abdulwakeel12/DIY-FAB-Transistor-Tester/images/Electrical PCB.jpg

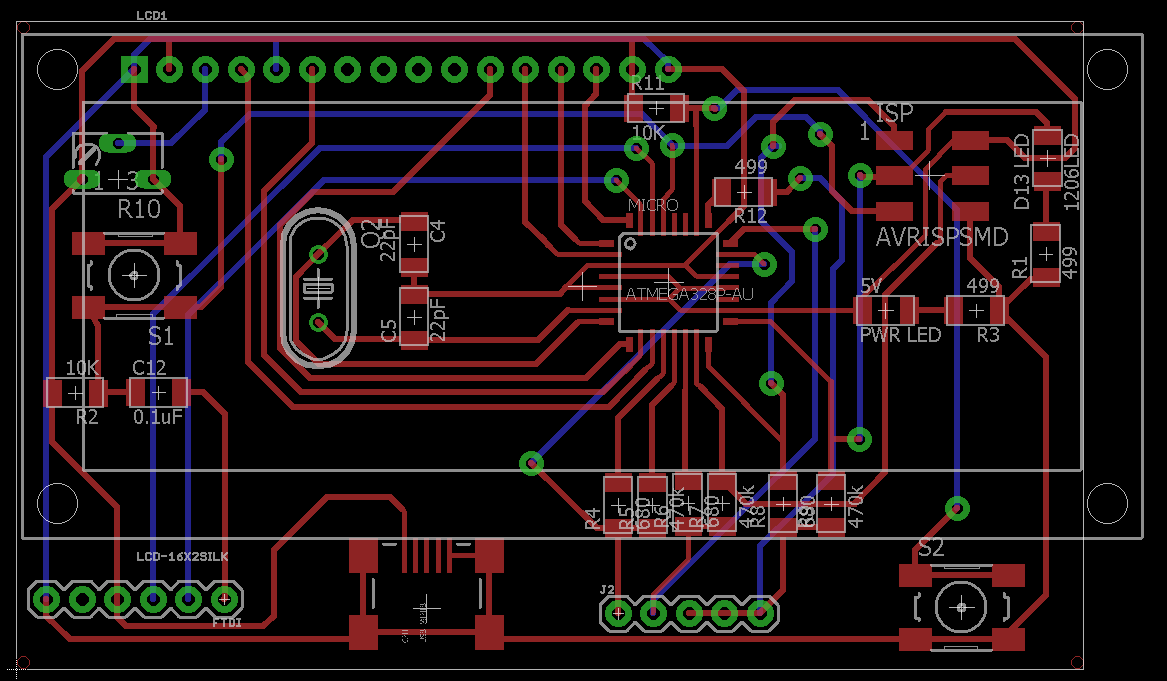
images/Electrical PCB.jpg
