abdulwakeel12/DIY-FAB-Transistor-Tester/images/Final Product 02.jpg

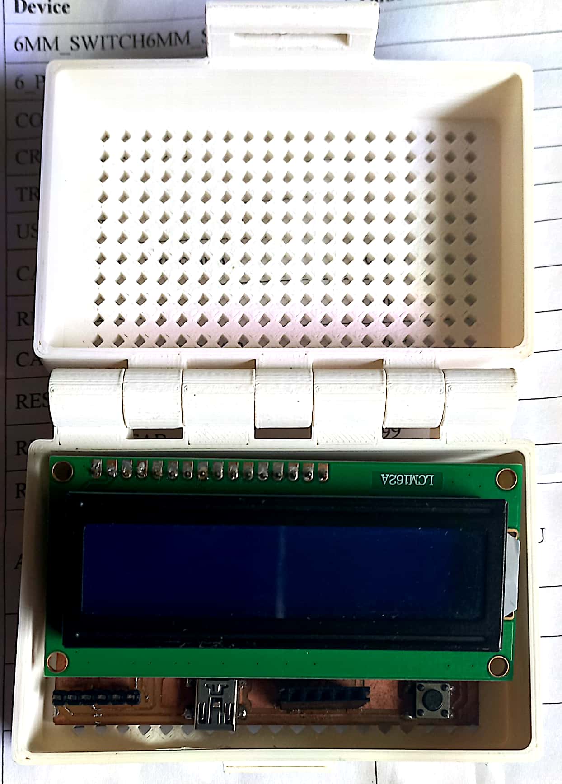
images/Final Product 02.jpg
