abdulwakeel12/DIY-FAB-Transistor-Tester/images/Final Product 03.jpg

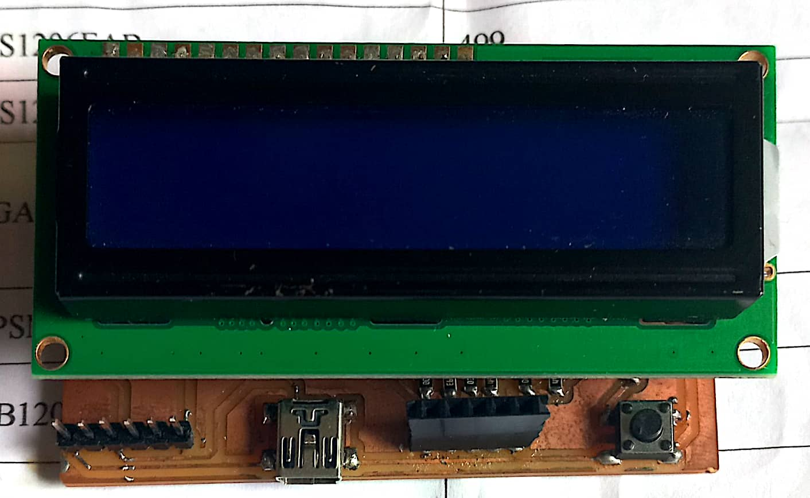
images/Final Product 03.jpg
