abdulwakeel12/DIY-FAB-Transistor-Tester/images/flow chart.jpg

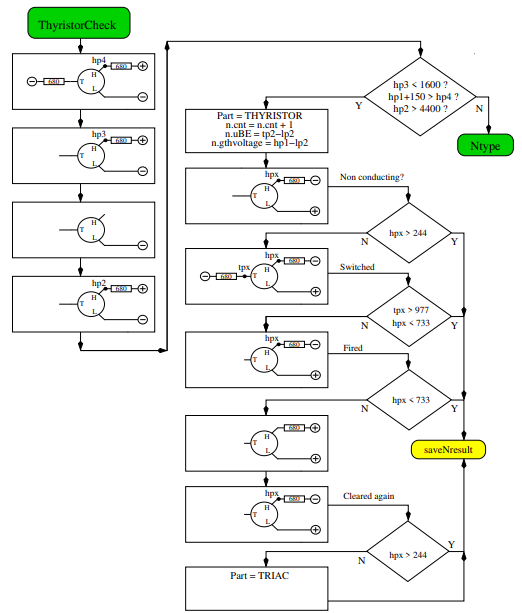
images/flow chart.jpg
