abdulwakeel12/DIY-FAB-Transistor-Tester/images/FTDI.jpg

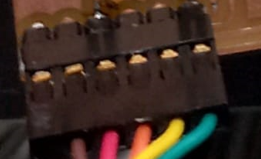
images/FTDI.jpg
