abdulwakeel12/DIY-FAB-Transistor-Tester/images/ICSP.jpg

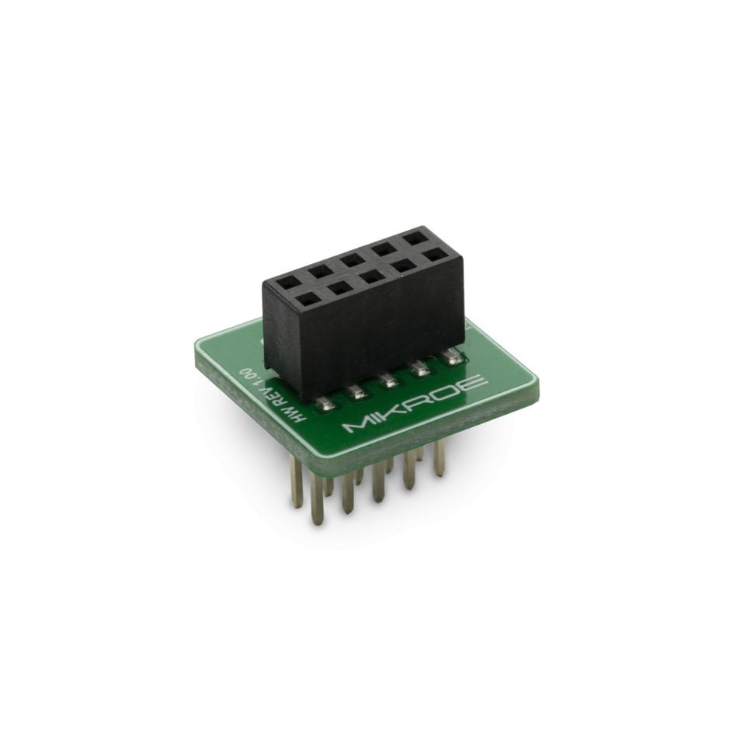
images/ICSP.jpg
