abdulwakeel12/DIY-FAB-Transistor-Tester/images/LCD.jpg

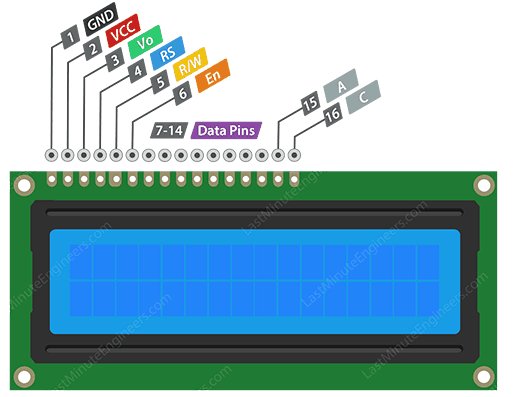
images/LCD.jpg
