abdulwakeel12/DIY-FAB-Transistor-Tester/images/Literature Review.jpg

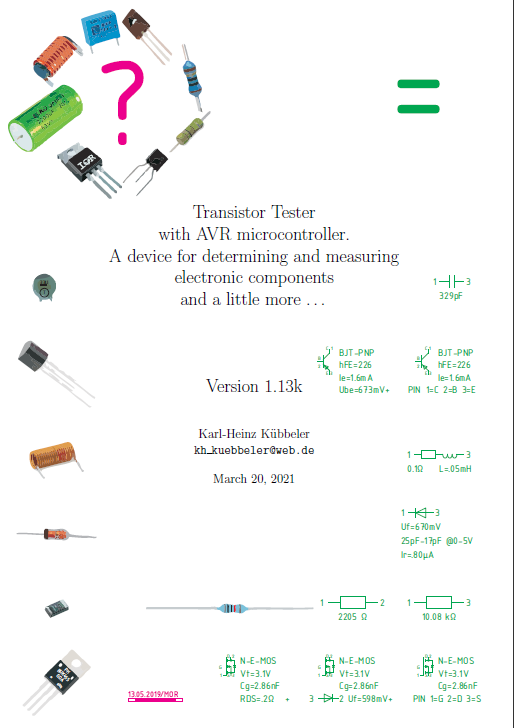
images/Literature Review.jpg
