abdulwakeel12/DIY-FAB-Transistor-Tester/images/Part 1.jpg

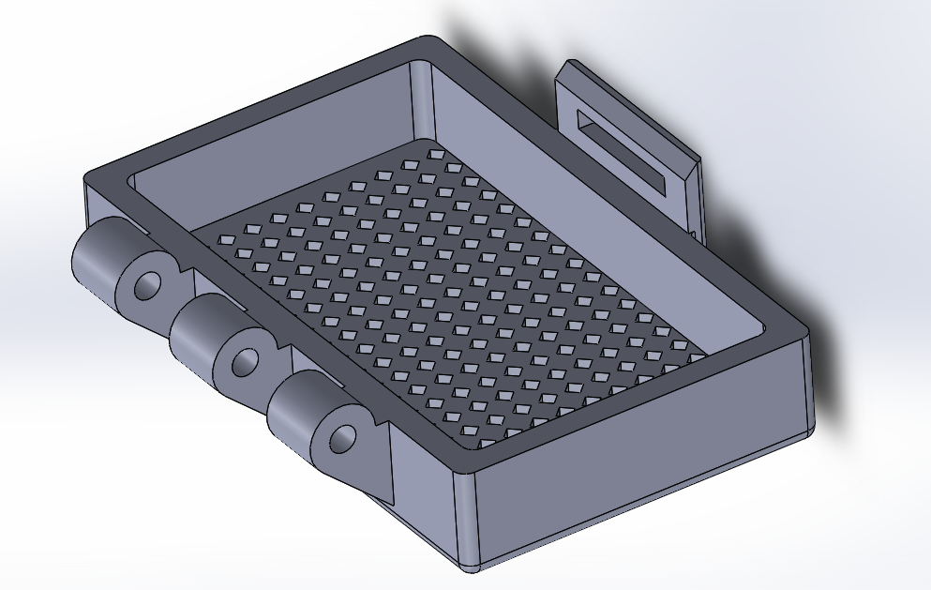
images/Part 1.jpg
