abdulwakeel12/DIY-FAB-Transistor-Tester/images/Part 2.jpg

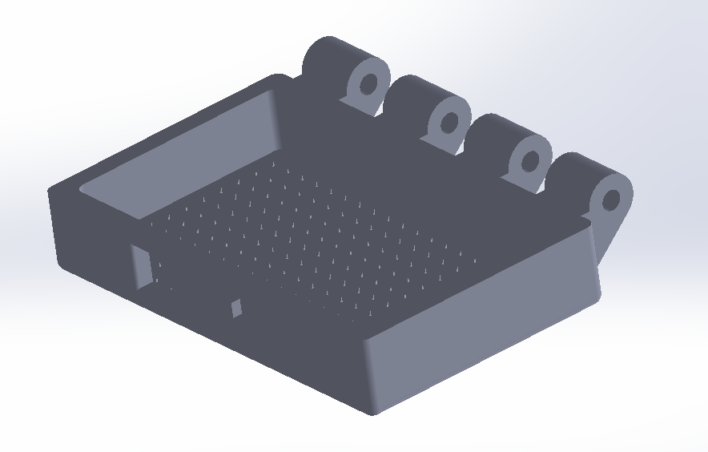
images/Part 2.jpg
