abdulwakeel12/DIY-FAB-Transistor-Tester/images/Part 3.jpg

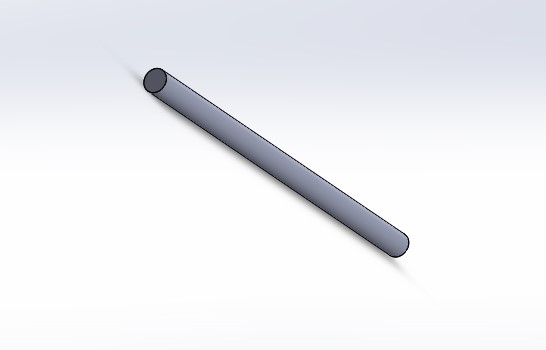
images/Part 3.jpg
