abdulwakeel12/DIY-FAB-Transistor-Tester/images/PCB Before Routing.jpg

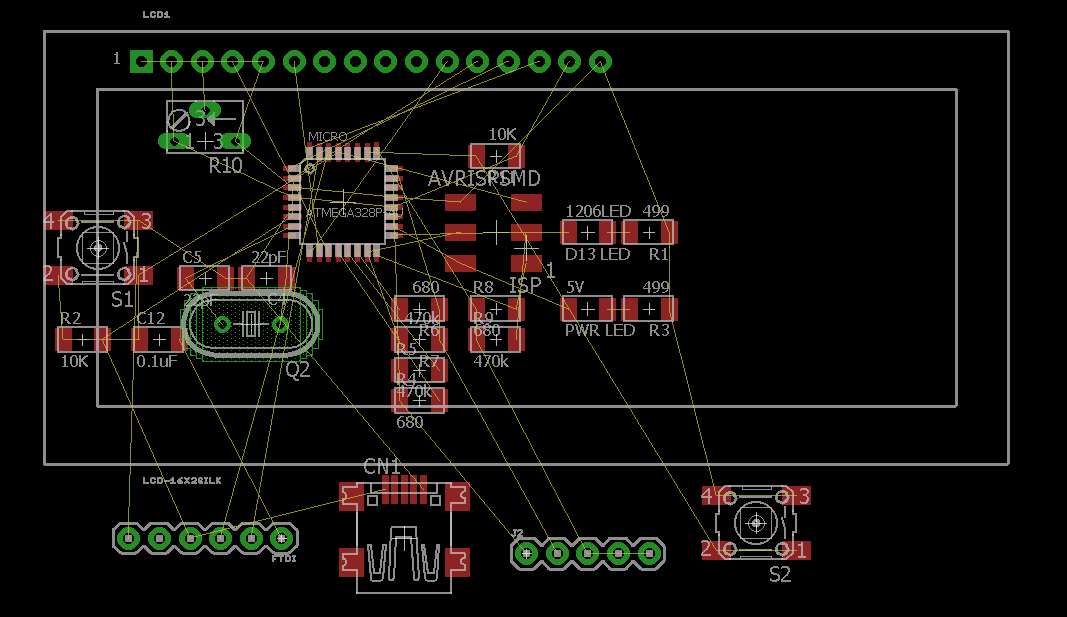
images/PCB Before Routing.jpg
