abdulwakeel12/DIY-FAB-Transistor-Tester/images/PCB BOTTOM.jpg

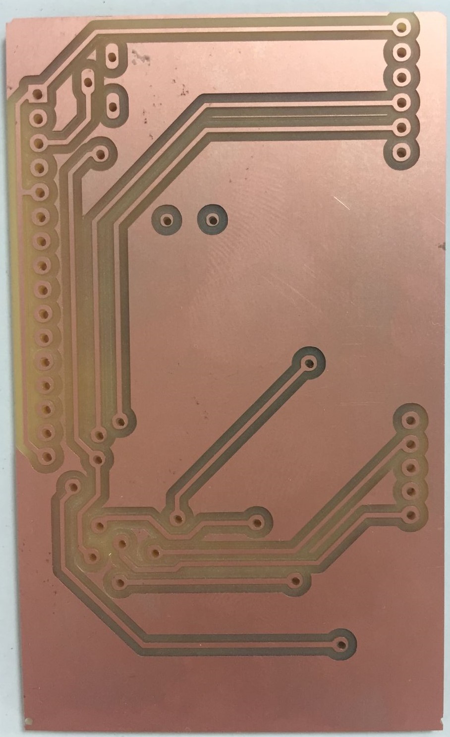
images/PCB BOTTOM.jpg
