abdulwakeel12/DIY-FAB-Transistor-Tester/images/PCB Top.jpg

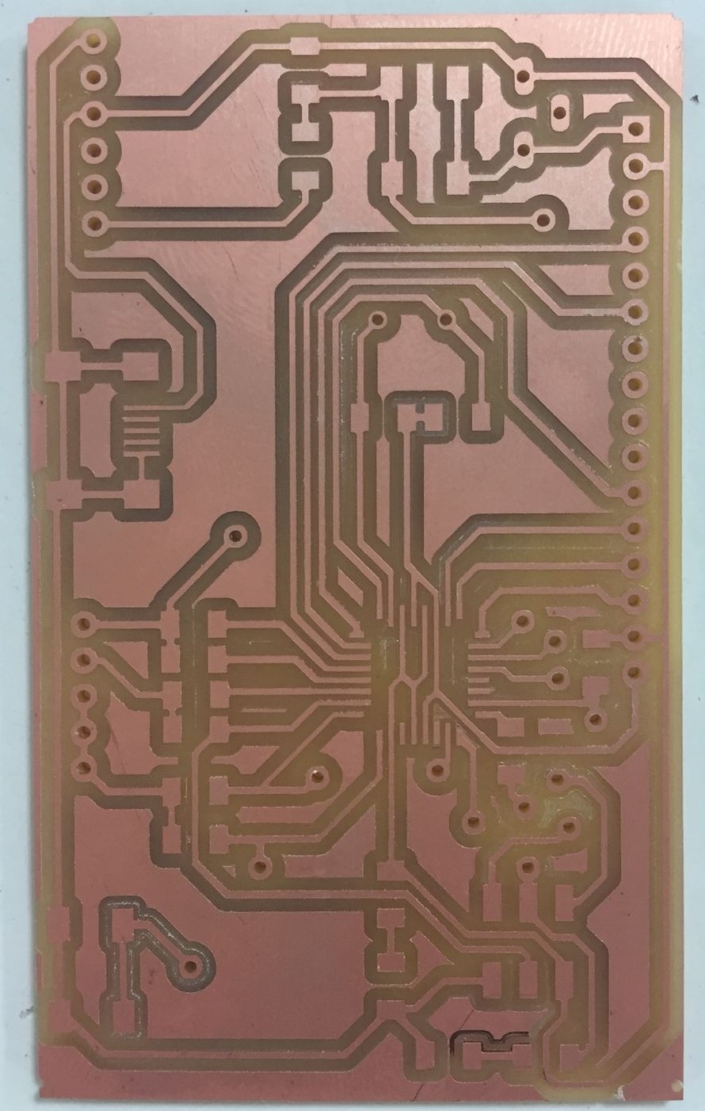
images/PCB Top.jpg
