abdulwakeel12/DIY-FAB-Transistor-Tester/images/Populated circuit.jpg

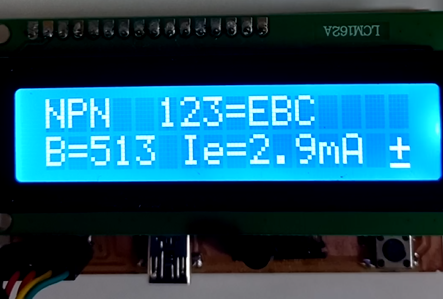
images/Populated circuit.jpg
