abdulwakeel12/DIY-FAB-Transistor-Tester/images/Populated pcb.jpg

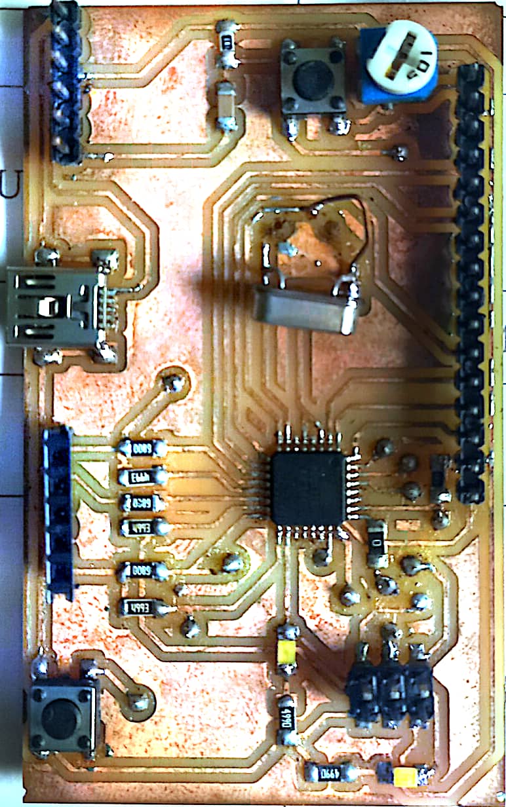
images/Populated pcb.jpg
