abdulwakeel12/DIY-FAB-Transistor-Tester/images/SRM Machine.jpg

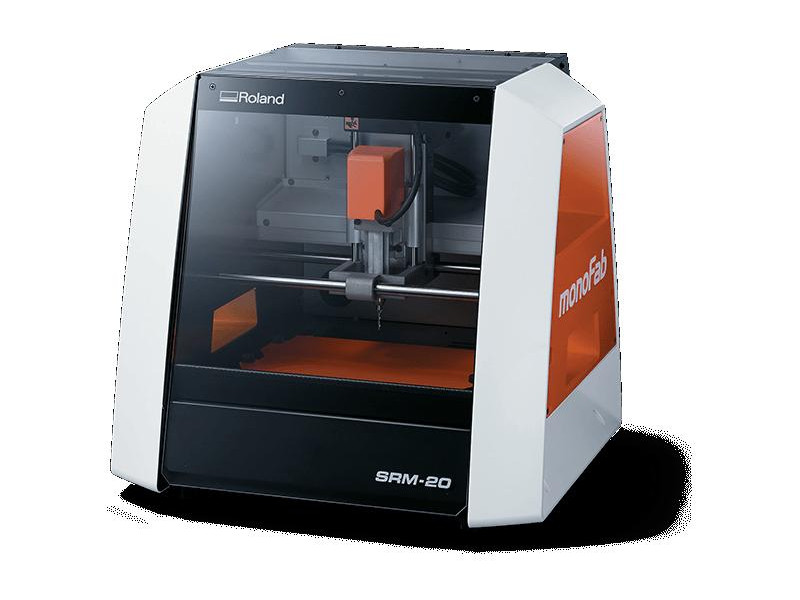
images/SRM Machine.jpg
