abdulwakeel12/DIY-FAB-Transistor-Tester/images/tactile.jpg

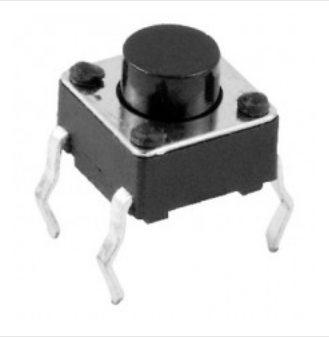
images/tactile.jpg
