abdulwakeel12/DIY-FAB-Transistor-Tester/images/Ultimaker in Lab.jpg

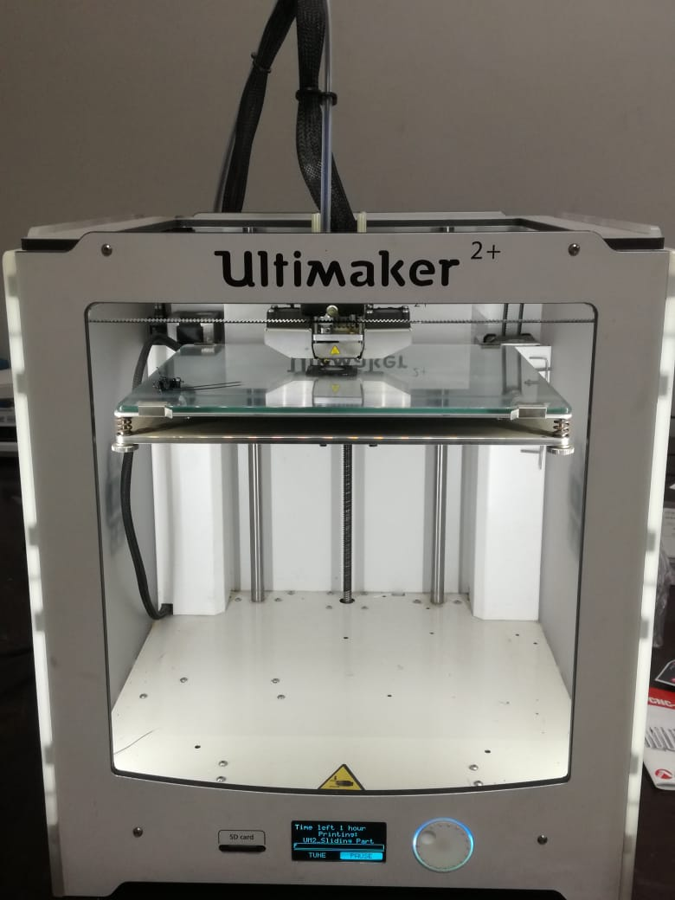
images/Ultimaker in Lab.jpg
