abdulwakeel12/DIY-FAB-Transistor-Tester/images/Ultimaker.jpg

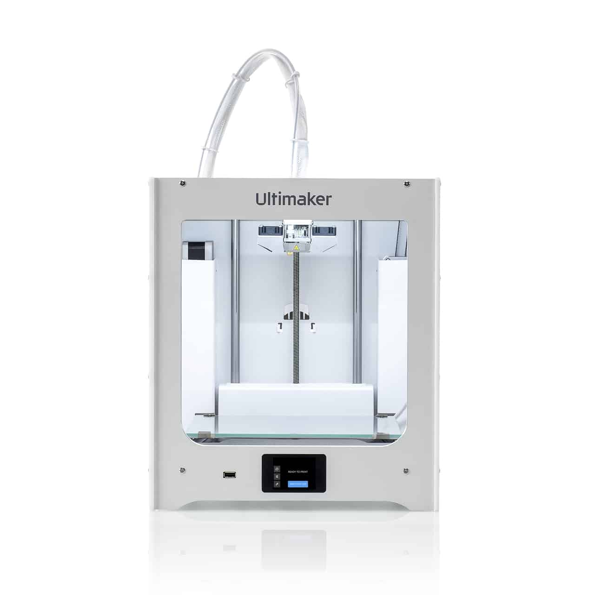
images/Ultimaker.jpg
