abdulwakeel12/DIY-FAB-Transistor-Tester/images/3D Printed Part 01.jpg

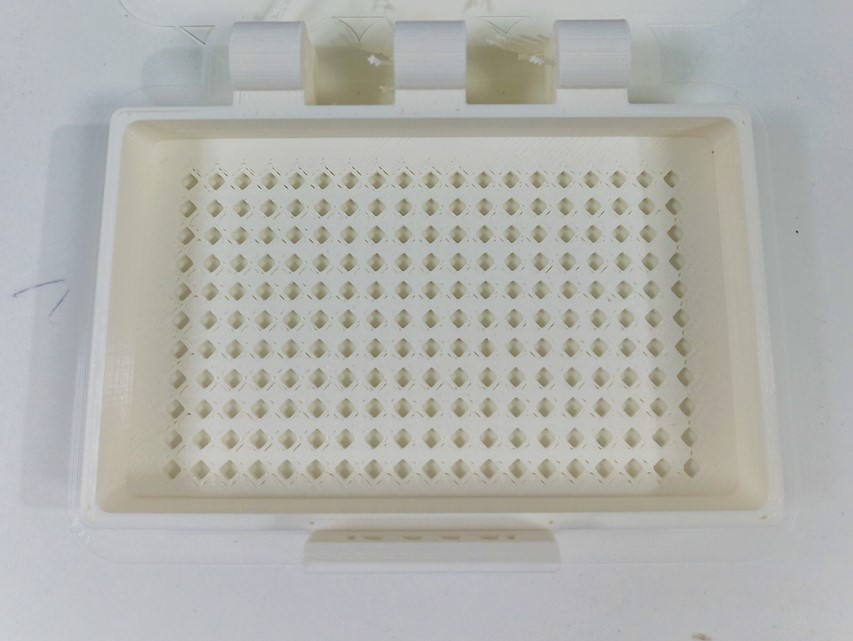
images/3D Printed Part 01.jpg
