abdulwakeel12/DIY-FAB-Transistor-Tester/images/Assembly part 1.jpg

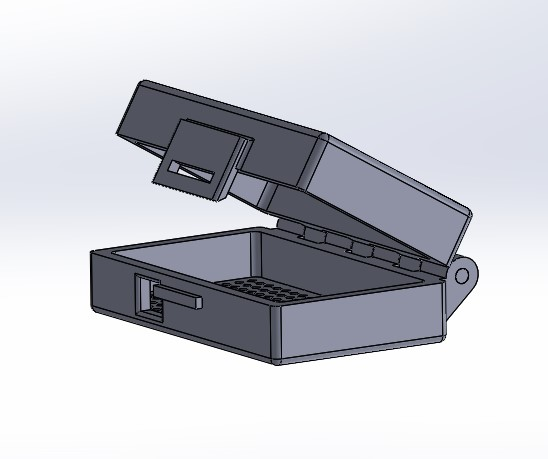
images/Assembly part 1.jpg
