abdulwakeel12/DIY-FAB-Transistor-Tester/images/Assembly part 2.jpg

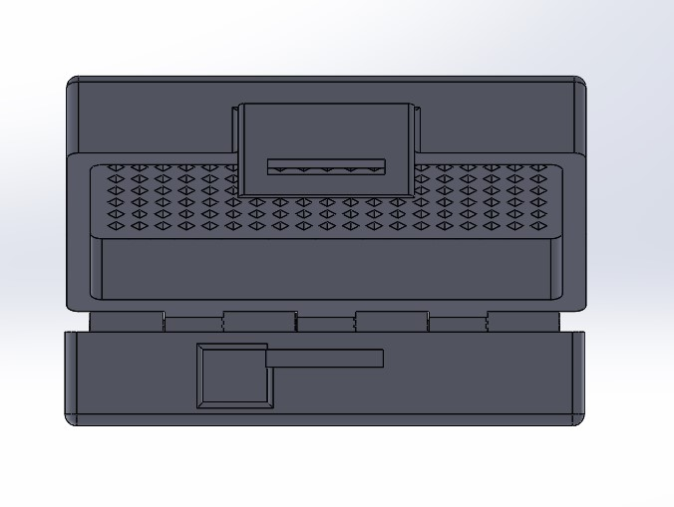
images/Assembly part 2.jpg
