abdulwakeel12/DIY-FAB-Transistor-Tester/images/Assembly part 3.jpg

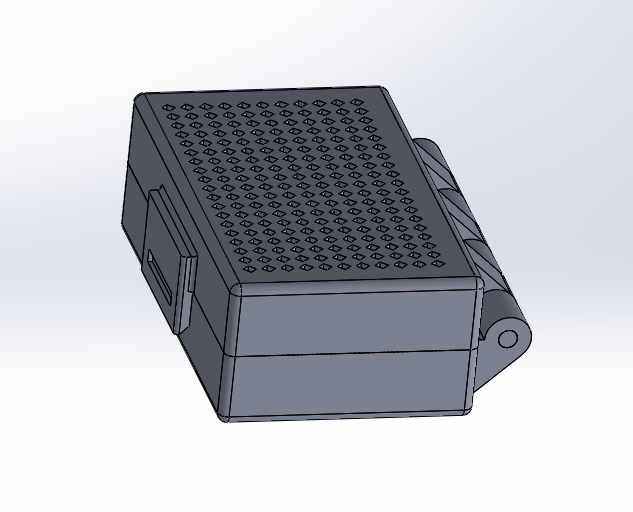
images/Assembly part 3.jpg
