abdulwakeel12/DIY-FAB-Transistor-Tester/images/Operating TT 1.jpg

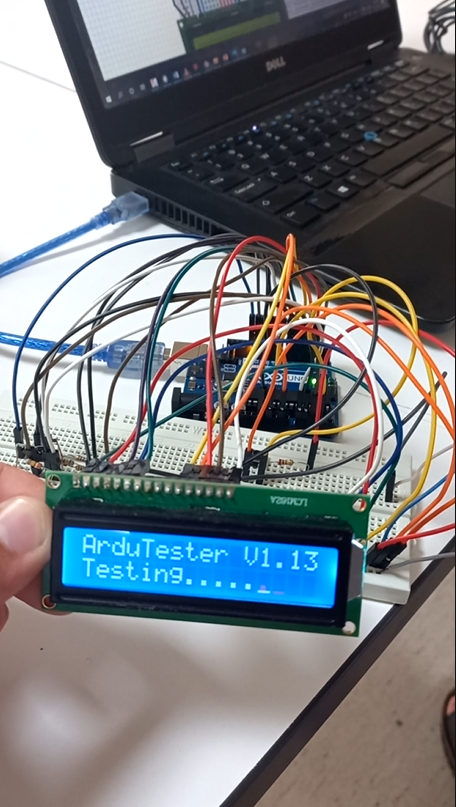
images/Operating TT 1.jpg
