abdulwakeel12/DIY-FAB-Transistor-Tester/images/Operating TT 3.jpg

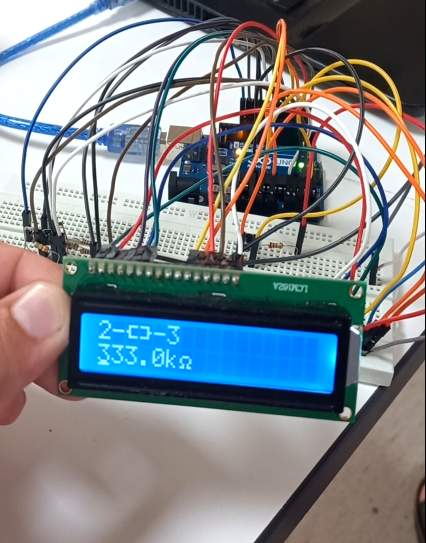
images/Operating TT 3.jpg
