abdulwakeel12/DIY-FAB-Transistor-Tester/images/Program.jpg

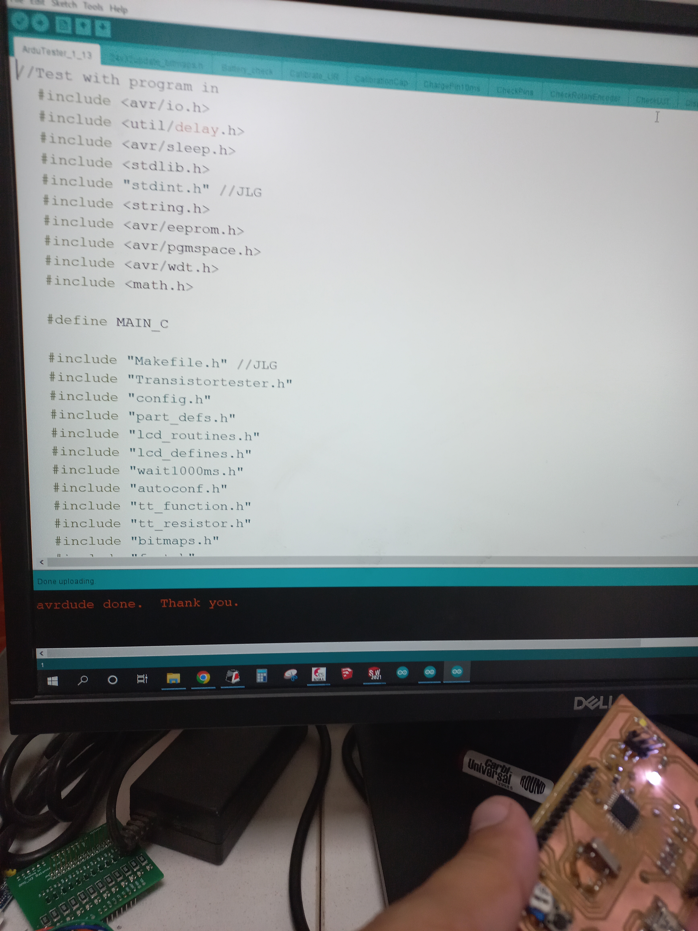
images/Program.jpg
