abdulwakeel12/DIY-FAB-Transistor-Tester/images/3D Printing Process Pic.jpg

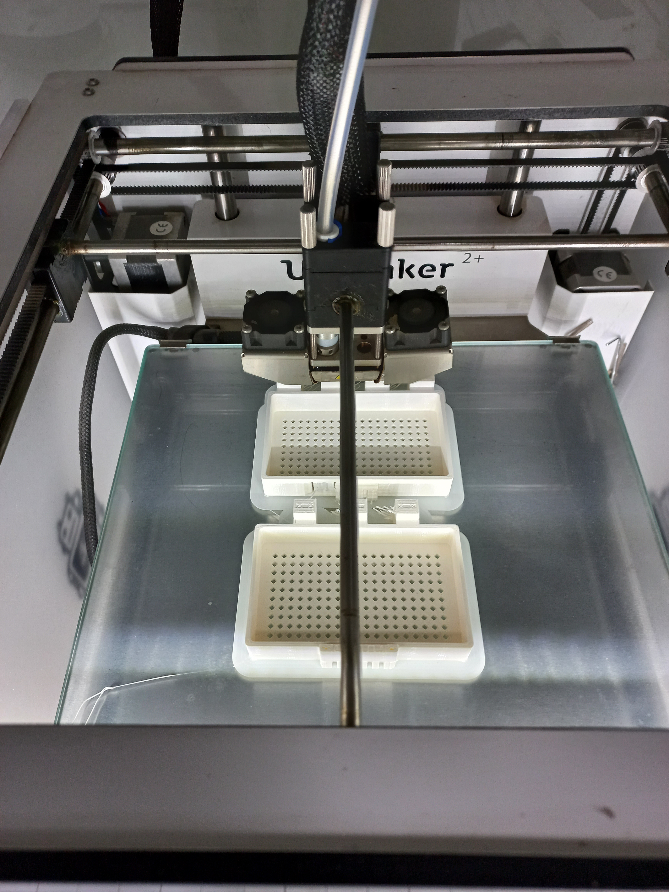
images/3D Printing Process Pic.jpg
